bitraf/bitraf-cnc/docs/shopbot/Bitraf/images/Shopbot_24v_og_5v_psu.jpg

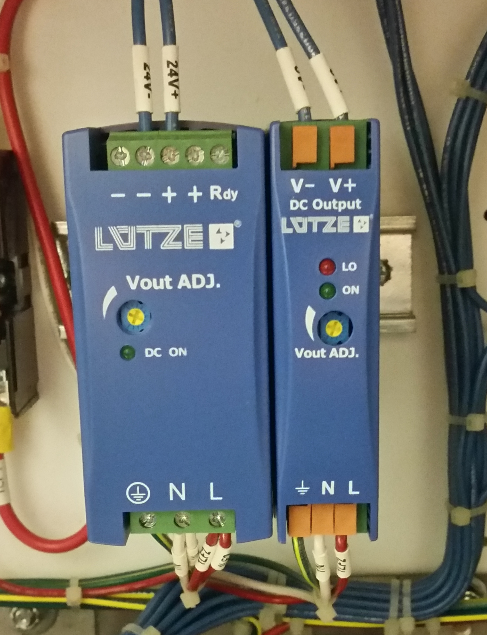
docs/shopbot/Bitraf/images/Shopbot_24v_og_5v_psu.jpg
