bitraf/bitraf-cnc/docs/shopbot/Bitraf/images/Shopbot_kontakter_driver-kort.jpg

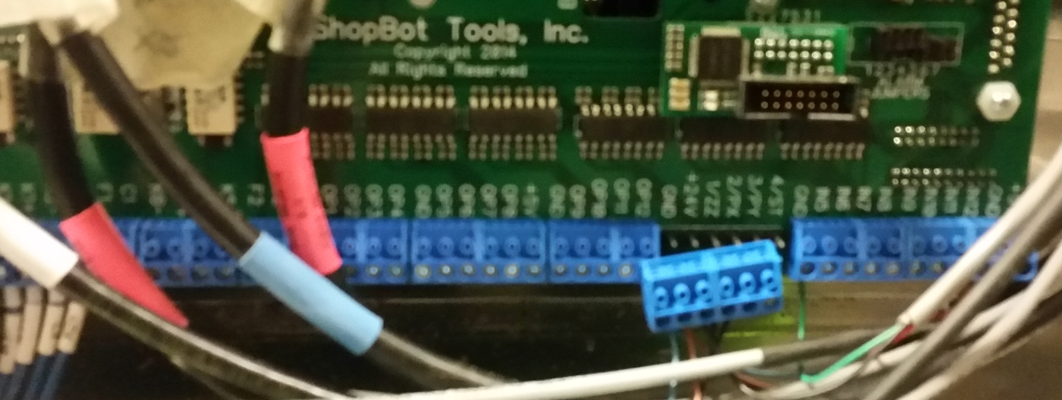
docs/shopbot/Bitraf/images/Shopbot_kontakter_driver-kort.jpg
