bitraf/bitraf-cnc/docs/shopbot/Bitraf/images/Shopbot_kontroller-kort.jpg

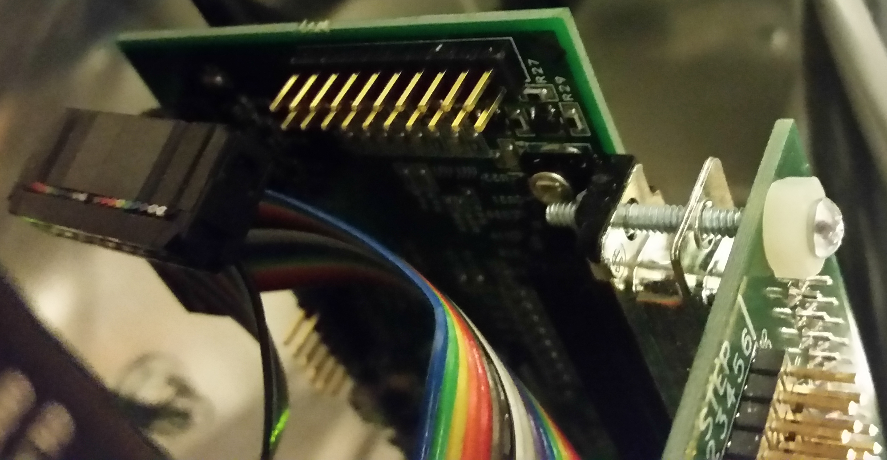
docs/shopbot/Bitraf/images/Shopbot_kontroller-kort.jpg
