bitraf/bitraf-cnc/docs/shopbot/Bitraf/images/Shopbot_VFD.jpg

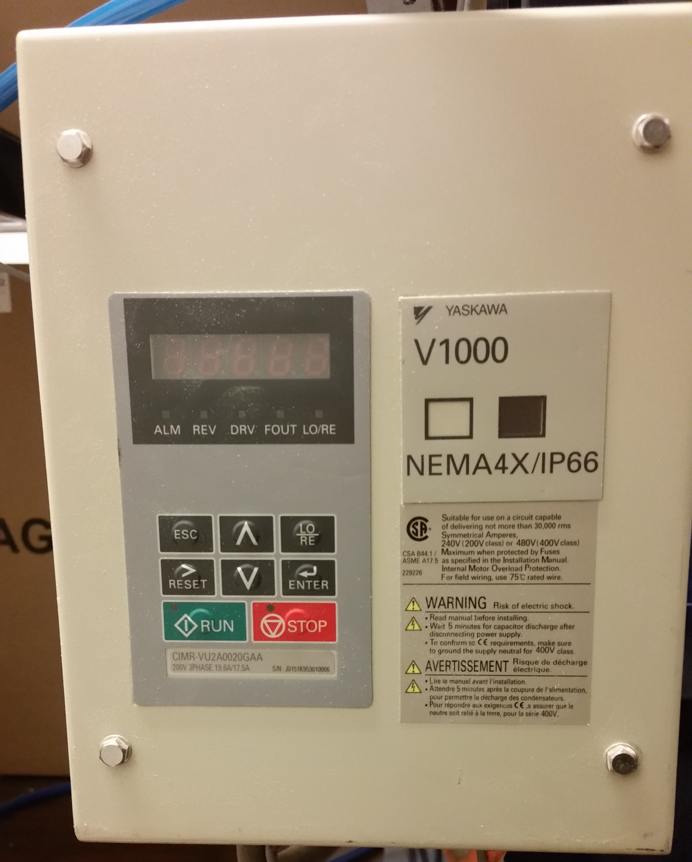
docs/shopbot/Bitraf/images/Shopbot_VFD.jpg
