bitraf/bitraf-cnc/docs/shopbot/Bitraf/images/Shopbot_VFD_detail.jpg

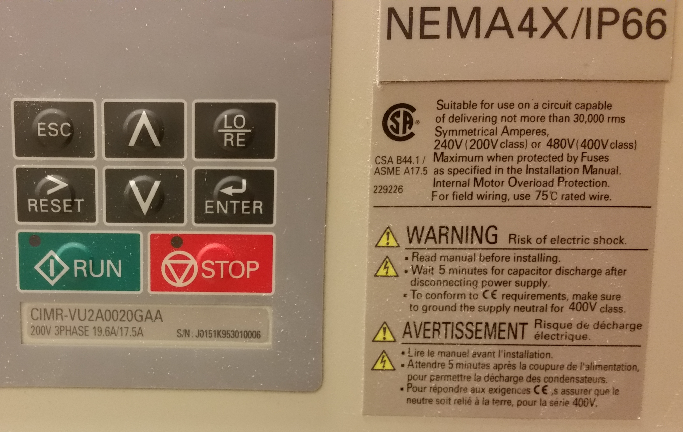
docs/shopbot/Bitraf/images/Shopbot_VFD_detail.jpg
