bitraf/bitraf-cnc/img/control_VFD_circuit.JPG

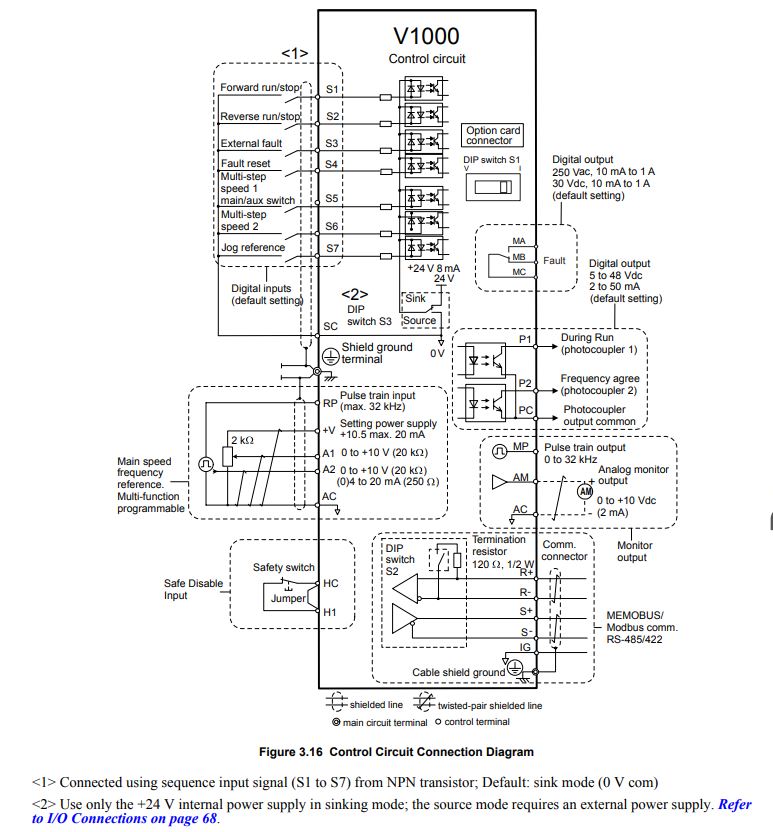
img/control_VFD_circuit.JPG
