bitraf/bitraf-cnc/docs/shopbot/Bitraf/wiring_diagrams/ShopBot_Power_Diagram.jpg

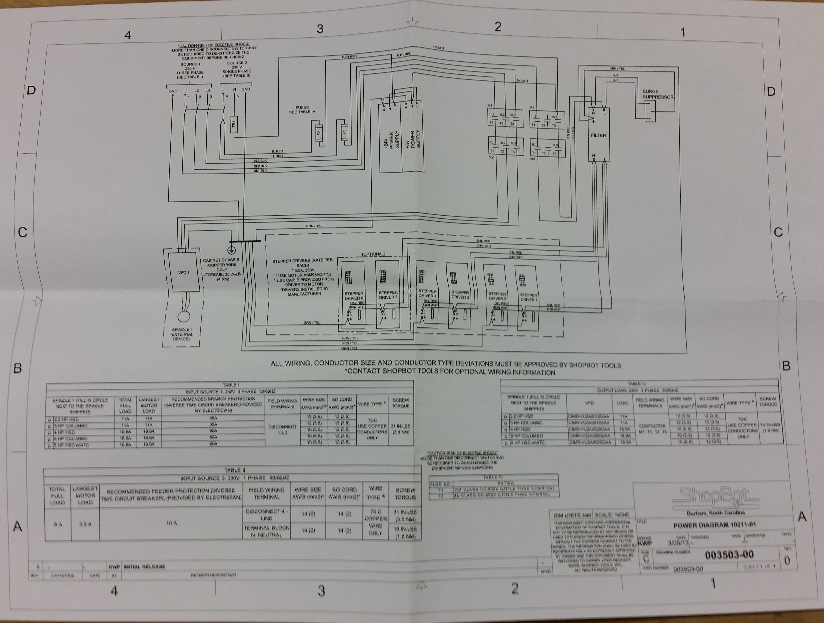
docs/shopbot/Bitraf/wiring_diagrams/ShopBot_Power_Diagram.jpg
