bitraf/bitraf-cnc/testing/20181018_PCB-milling-test_on_Hattori/images/bit_straight_0.4mm_1.jpg

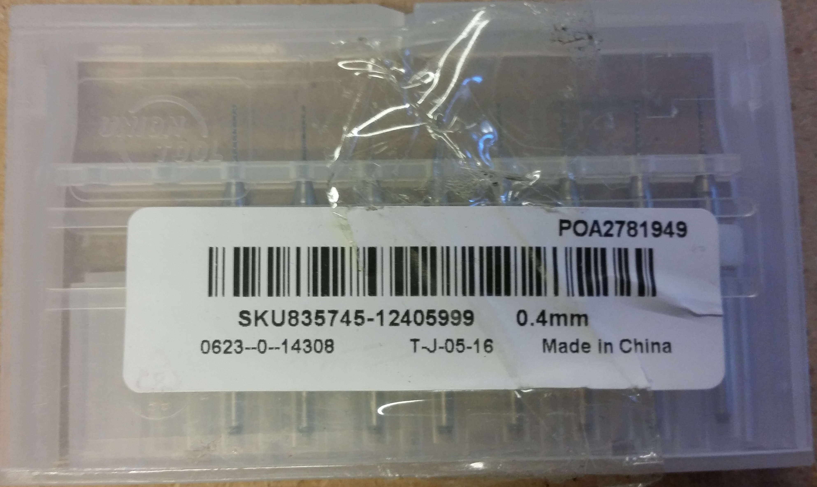
testing/20181018_PCB-milling-test_on_Hattori/images/bit_straight_0.4mm_1.jpg
