bitraf/bitraf-cnc/testing/20181018_PCB-milling-test_on_Hattori/images/bit_v-shaped_30_degrees_0.2mm_2.jpg

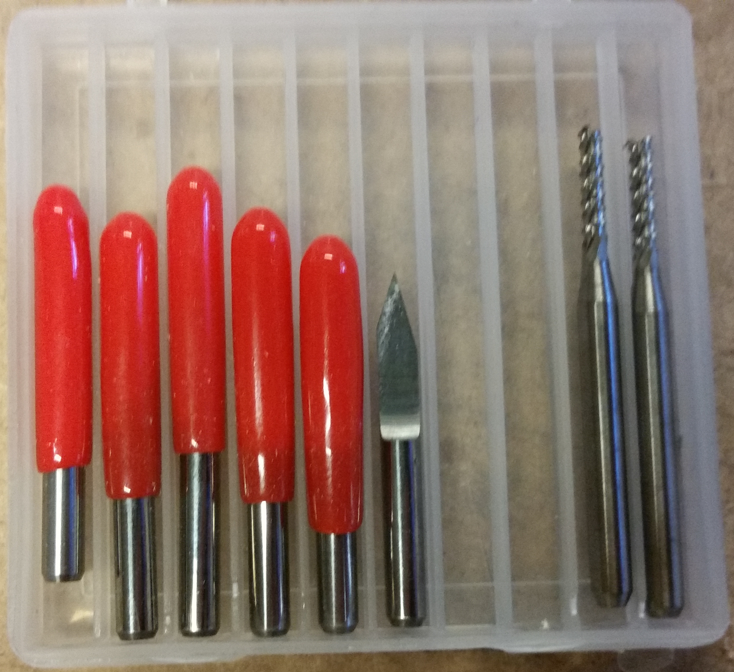
testing/20181018_PCB-milling-test_on_Hattori/images/bit_v-shaped_30_degrees_0.2mm_2.jpg
