bitraf/bitraf-cnc/testing/20181018_PCB-milling-test_on_Hattori/images/milling_1_20181018_221703.jpg

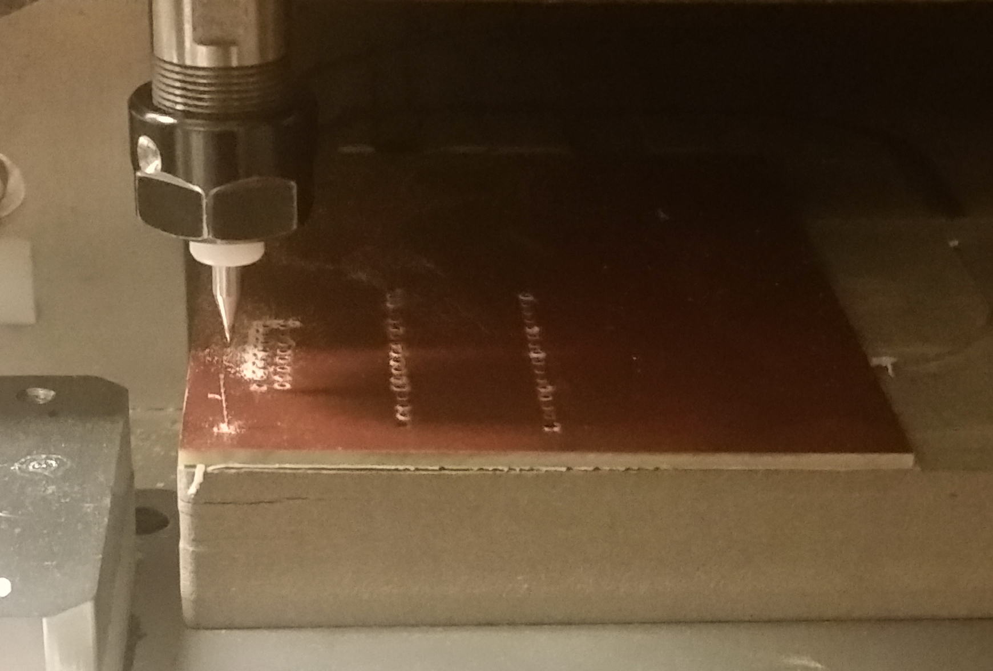
testing/20181018_PCB-milling-test_on_Hattori/images/milling_1_20181018_221703.jpg
