bitraf/bitraf-cnc/testing/20181018_PCB-milling-test_on_Hattori/images/result_1_20181018_223329.jpg

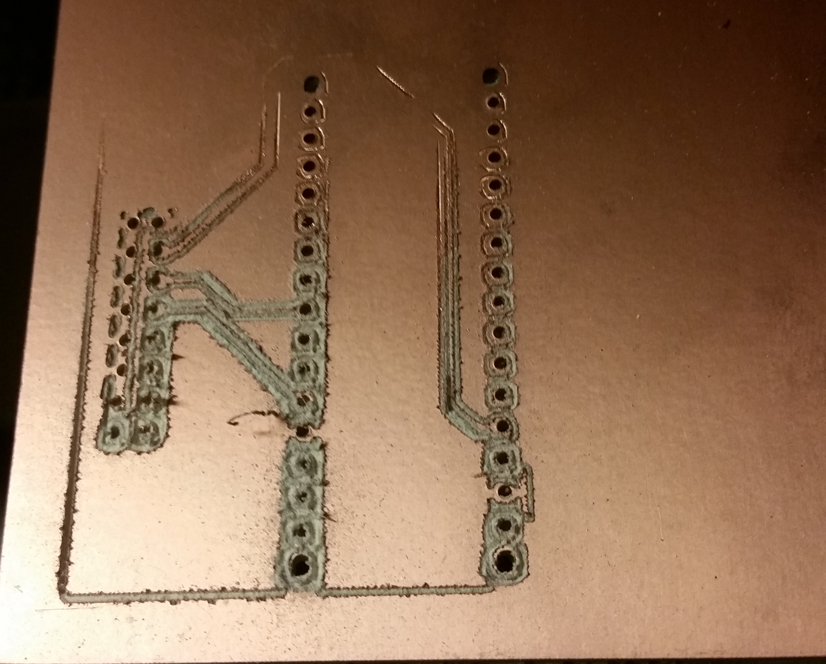
testing/20181018_PCB-milling-test_on_Hattori/images/result_1_20181018_223329.jpg
