bitraf/bitraf-cnc/testing/20181018_PCB-milling-test_on_Hattori/images/result_2_20181018_223333.jpg

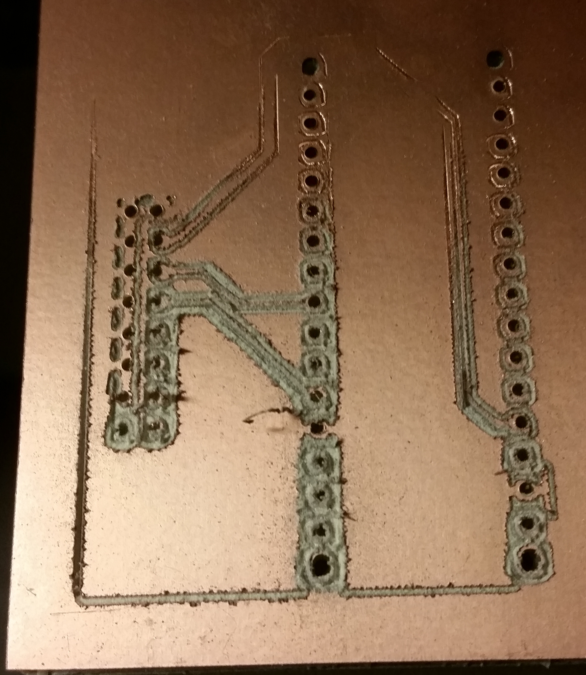
testing/20181018_PCB-milling-test_on_Hattori/images/result_2_20181018_223333.jpg
