bitraf/bitraf-cnc/testing/20181018_PCB-milling-test_on_Hattori/images/result_3_20181018_230134.jpg

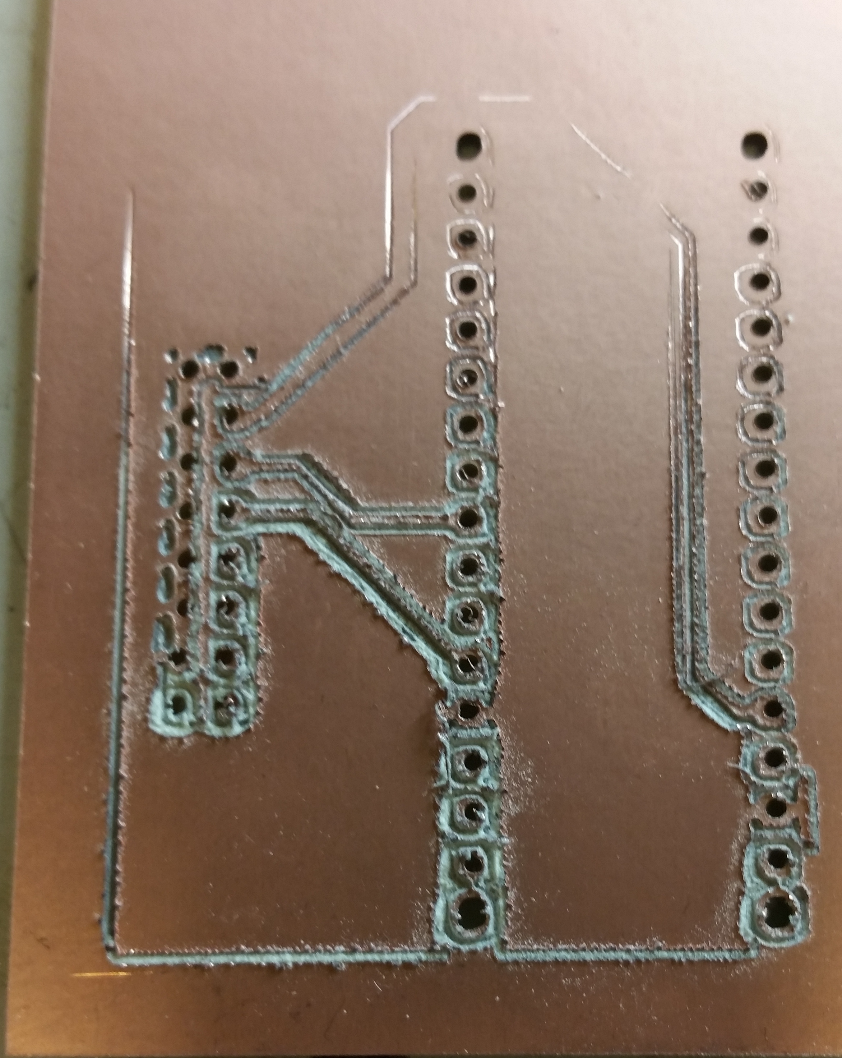
testing/20181018_PCB-milling-test_on_Hattori/images/result_3_20181018_230134.jpg
