bitraf/bitraf-cnc/testing/20181018_PCB-milling-test_on_Hattori/images/result_4_20181018_230139.jpg

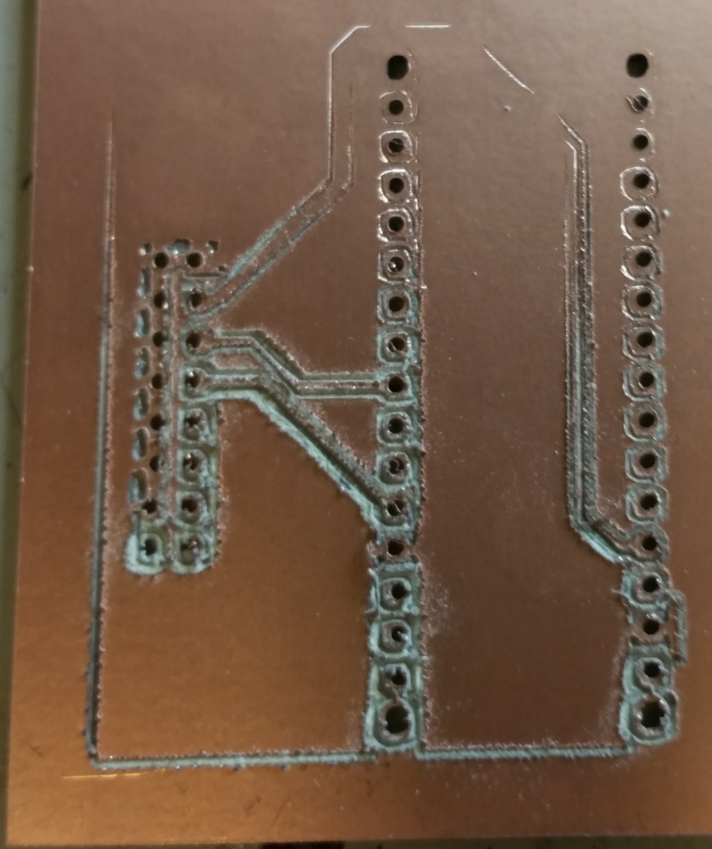
testing/20181018_PCB-milling-test_on_Hattori/images/result_4_20181018_230139.jpg
