bitraf/bitraf-cnc/testing/20181024_PCB-milling-test-2_on_Hattori/images/drilling_holes_1.jpg

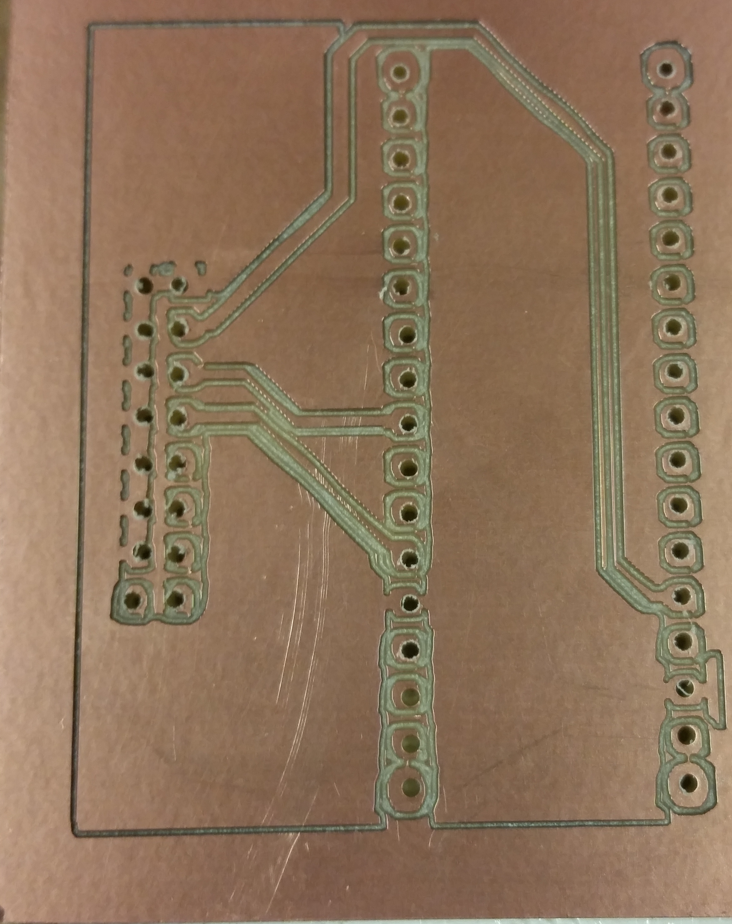
testing/20181024_PCB-milling-test-2_on_Hattori/images/drilling_holes_1.jpg
