bitraf/bitraf-cnc/testing/20181024_PCB-milling-test-2_on_Hattori/images/finished_PCB.jpg

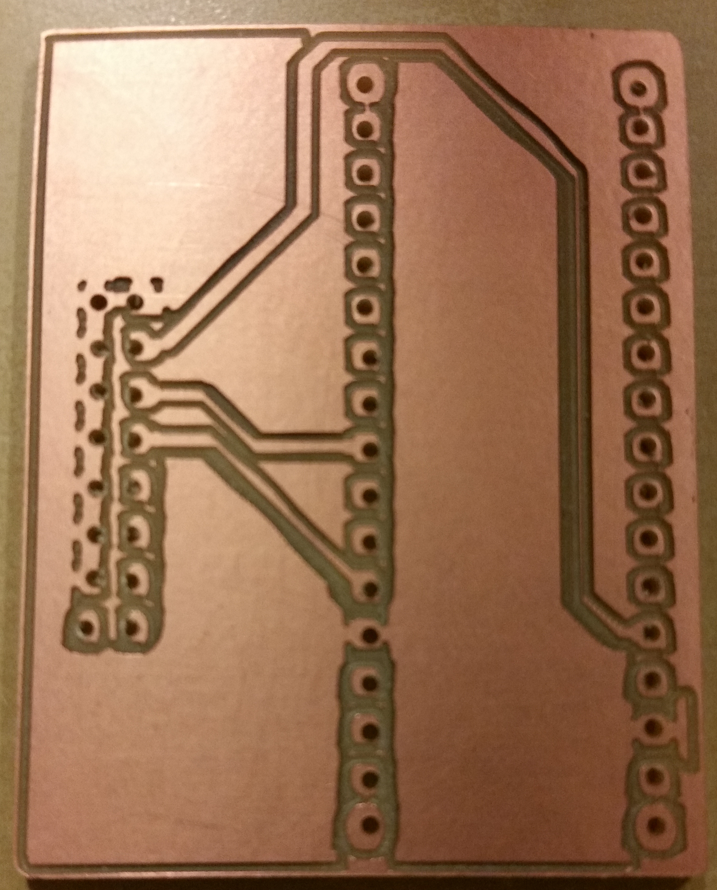
testing/20181024_PCB-milling-test-2_on_Hattori/images/finished_PCB.jpg
