bitraf/bitraf-cnc/testing/20181024_PCB-milling-test-2_on_Hattori/images/milling_tracks_2.jpg

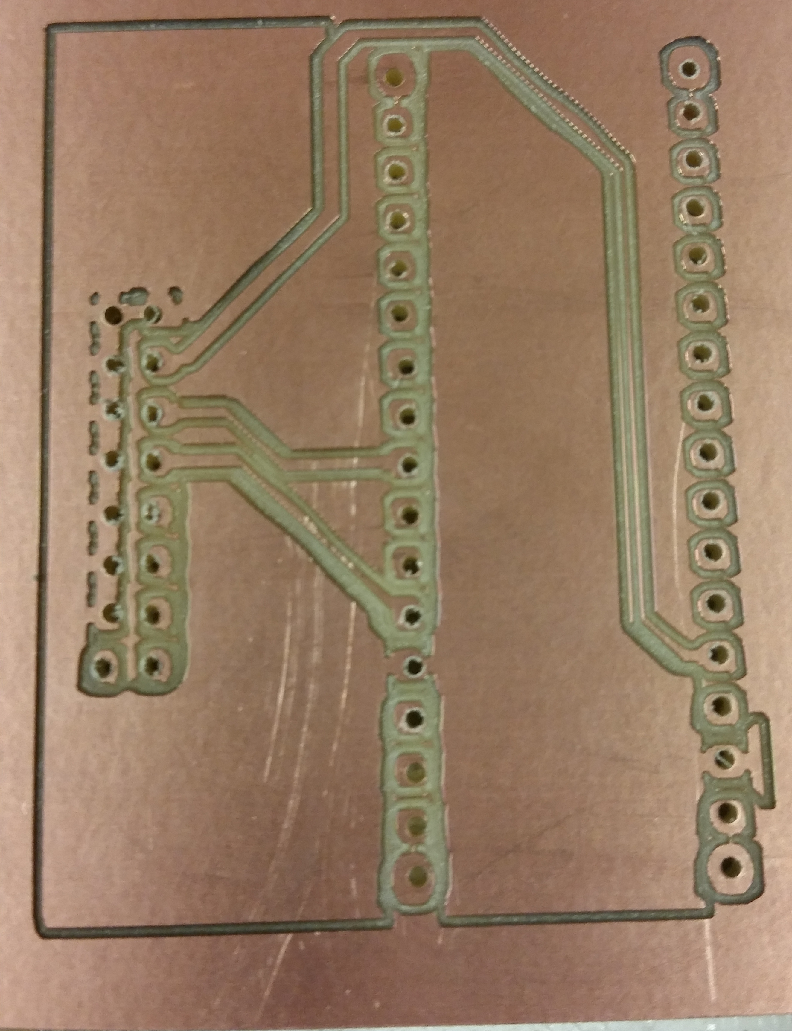
testing/20181024_PCB-milling-test-2_on_Hattori/images/milling_tracks_2.jpg
