bitraf/bitraf-cnc/testing/20181024_PCB-milling-test-2_on_Hattori/images/Hattori_chamferrail_bed_problems_fixed.jpg

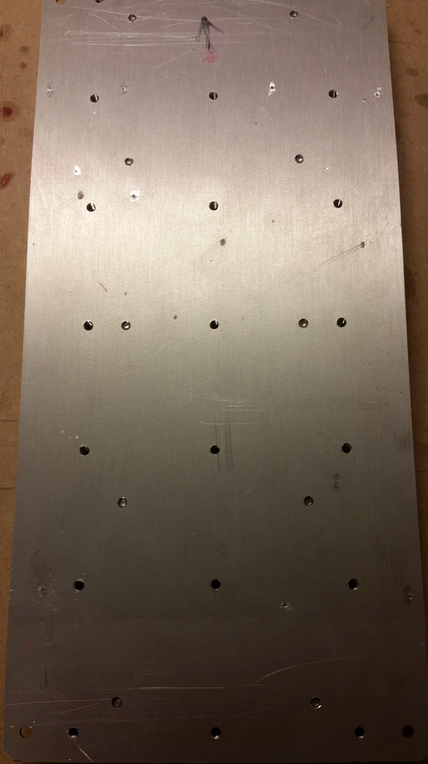
testing/20181024_PCB-milling-test-2_on_Hattori/images/Hattori_chamferrail_bed_problems_fixed.jpg
